chinmaypai642/stream_deck/firmware/deck_s3/bitmaps.h

#ifndef BITMAPS_H
#define BITMAPS_H

#include <Arduino.h>

// Volume Up Icon - 16x16 pixels
const unsigned char volume_up_icon [] PROGMEM = {
  0x00, 0x00, 0x00, 0x40, 0x00, 0xe0, 0x01, 0xe0,
  0x7f, 0xe4, 0xff, 0xec, 0xff, 0xec, 0xff, 0xec,
  0xff, 0xec, 0xff, 0xec, 0x7f, 0xe4, 0x01, 0xe0,
  0x00, 0xe0, 0x00, 0x40, 0x00, 0x00, 0x00, 0x00
};

// Volume Down Icon - 16x16 pixels
const unsigned char volume_down_icon [] PROGMEM = {
  0x00, 0x00, 0x00, 0x00, 0x00, 0x00, 0x00, 0x00,
  0x7f, 0xe0, 0xff, 0xf0, 0xff, 0xf8, 0xff, 0xfc,
  0xff, 0xfc, 0xff, 0xf8, 0x7f, 0xf0, 0x00, 0xe0,
  0x00, 0x00, 0x00, 0x00, 0x00, 0x00, 0x00, 0x00
};

// Play Icon - 16x16 pixels
const unsigned char play_icon [] PROGMEM = {
  0x00, 0x00, 0x0c, 0x00, 0x1c, 0x00, 0x3c, 0x00,
  0x7c, 0x00, 0xfc, 0x00, 0xfc, 0x00, 0xfc, 0x00,
  0xfc, 0x00, 0xfc, 0x00, 0x7c, 0x00, 0x3c, 0x00,
  0x1c, 0x00, 0x0c, 0x00, 0x00, 0x00, 0x00, 0x00
};

// Pause Icon - 16x16 pixels
const unsigned char pause_icon [] PROGMEM = {
  0x00, 0x00, 0x3c, 0x3c, 0x3c, 0x3c, 0x3c, 0x3c,
  0x3c, 0x3c, 0x3c, 0x3c, 0x3c, 0x3c, 0x3c, 0x3c,
  0x3c, 0x3c, 0x3c, 0x3c, 0x3c, 0x3c, 0x3c, 0x3c,
  0x3c, 0x3c, 0x00, 0x00, 0x00, 0x00, 0x00, 0x00
};

// Eyes Open (32x16)
const unsigned char eye_open [] PROGMEM = {
  0x00, 0x00, 0x00, 0x00, 0x00, 0x3f, 0xfc, 0x00, 0x00, 0xff, 0xff, 0x00, 0x03, 0xff, 0xff, 0xc0,
  0x07, 0xff, 0xff, 0xe0, 0x0f, 0xff, 0xff, 0xf0, 0x1f, 0xfc, 0x3f, 0xf8, 0x1f, 0xf0, 0x0f, 0xf8,
  0x1f, 0xf0, 0x0f, 0xf8, 0x1f, 0xfc, 0x3f, 0xf8, 0x0f, 0xff, 0xff, 0xf0, 0x07, 0xff, 0xff, 0xe0,
  0x03, 0xff, 0xff, 0xc0, 0x00, 0xff, 0xff, 0x00, 0x00, 0x3f, 0xfc, 0x00, 0x00, 0x00, 0x00, 0x00
};

// Eyes Closed (32x16)
const unsigned char eye_closed [] PROGMEM = {
  0x00, 0x00, 0x00, 0x00, 0x00, 0x00, 0x00, 0x00, 0x00, 0x00, 0x00, 0x00, 0x00, 0x00, 0x00, 0x00,
  0x00, 0x00, 0x00, 0x00, 0x00, 0x00, 0x00, 0x00, 0x00, 0x00, 0x00, 0x00, 0x1f, 0xff, 0xff, 0xf8,
  0x1f, 0xff, 0xff, 0xf8, 0x00, 0x00, 0x00, 0x00, 0x00, 0x00, 0x00, 0x00, 0x00, 0x00, 0x00, 0x00,
  0x00, 0x00, 0x00, 0x00, 0x00, 0x00, 0x00, 0x00, 0x00, 0x00, 0x00, 0x00, 0x00, 0x00, 0x00, 0x00
};

#endif
